YuriySm/Ikoka-NanoX-Meshtastic-Device/media/1.1.2/Ikoka-NanoX-1.1.2-size.png

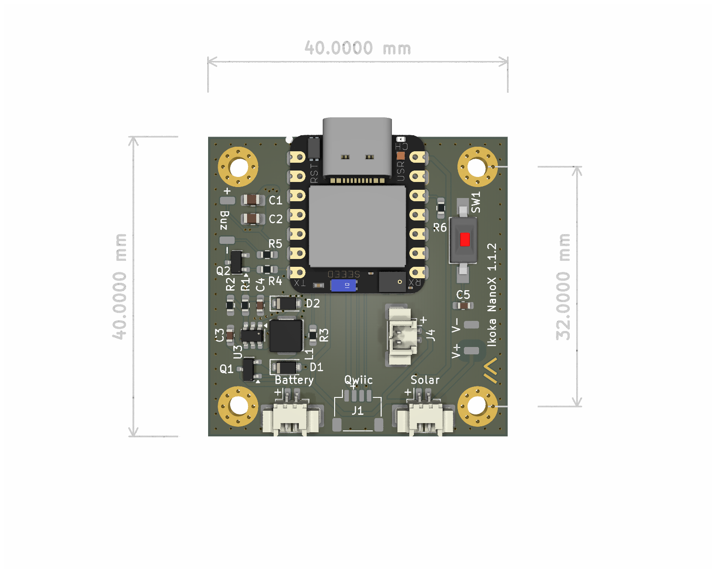
media/1.1.2/Ikoka-NanoX-1.1.2-size.png
